SirBramble/The-Macruwu-2.0/PCB/The Macruwu 2.0/Seeeduino XIAO KICAD/XIAO-ESP32C3-DXF/113991054/top.dxf

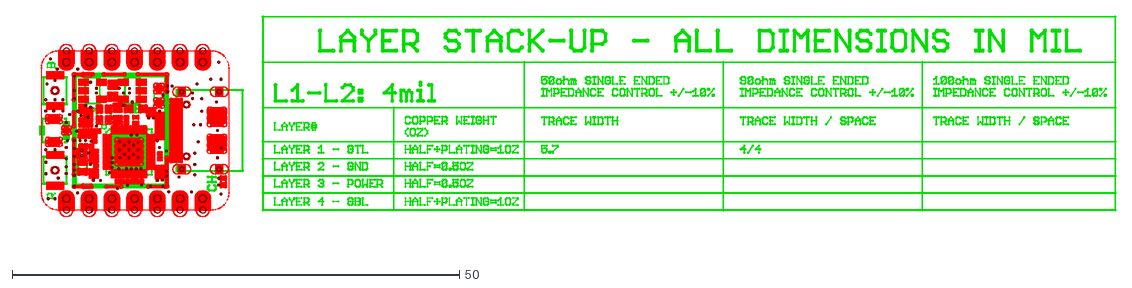
[picture p24: CAD file, 2023-02-24]
PCB/The Macruwu 2.0/Seeeduino XIAO KICAD/XIAO-ESP32C3-DXF/113991054/top.dxf
122.9 x 25.9
