SirBramble/The-Macruwu-2.0/3D Moddels/Case/Base no battery/Part1 no headphone.STL

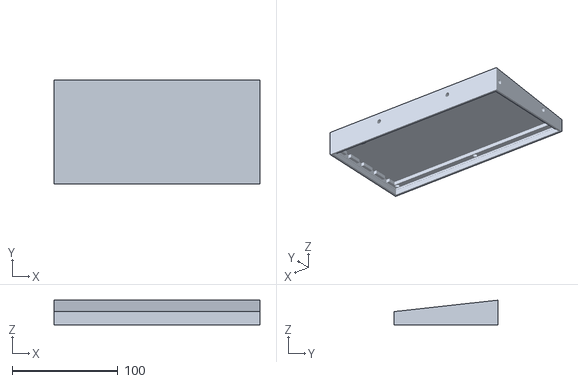
[picture p25: CAD file, 2024-02-04]
3D Moddels/Case/Base no battery/Part1 no headphone.STL
195.0 x 98.3 x 23.4
