SirBramble/The-Macruwu-2.0/3D Moddels/Case/Base/Plate.SLDPRT

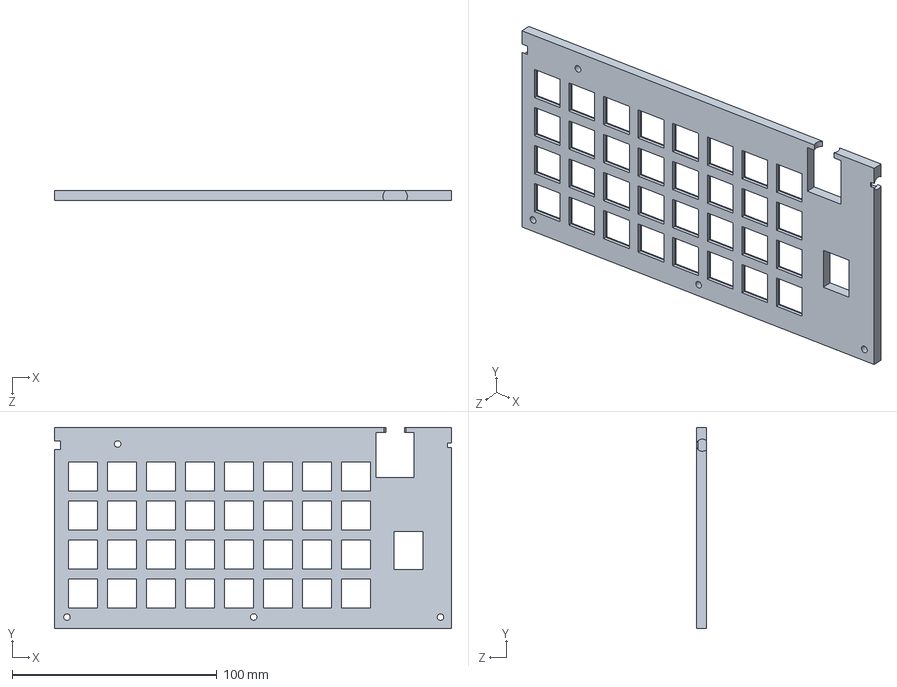
[picture p26: CAD file, 2023-02-24]
3D Moddels/Case/Base/Plate.SLDPRT
194.0 x 98.3 x 4.80 mm
