SirBramble/The-Macruwu-2.0/3D Moddels/Case/Base no battery/Part1.SLDPRT

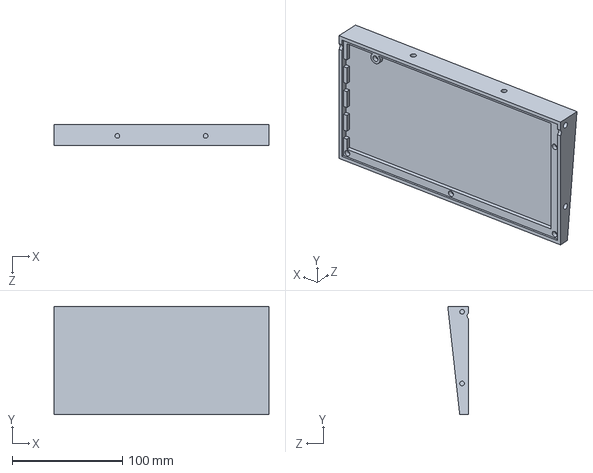
[picture p27: CAD file, 2024-02-04]
3D Moddels/Case/Base no battery/Part1.SLDPRT
195.0 x 98.3 x 18.6 mm
