SirBramble/The-Macruwu-2.0/3D Moddels/Case/Base/LED Cover.SLDPRT

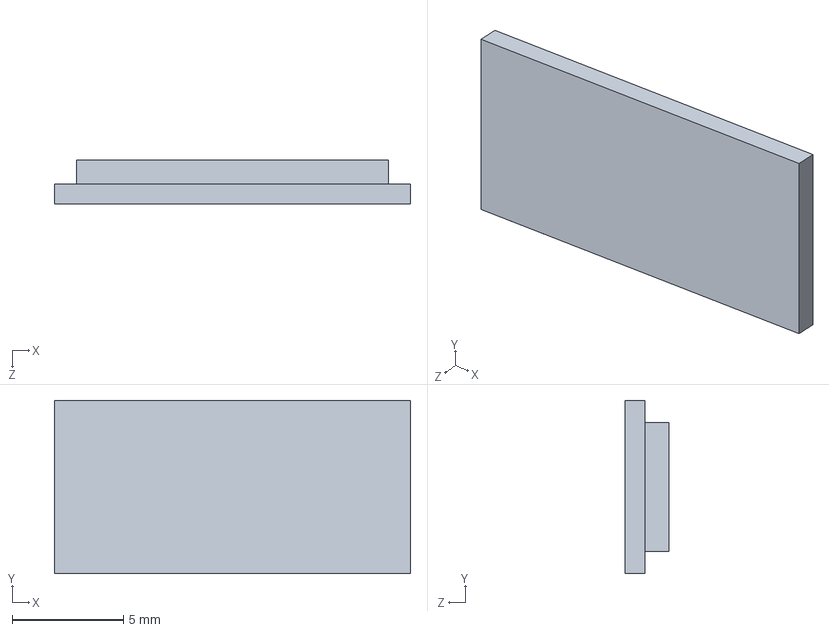
[picture p28: CAD file, 2023-02-24]
3D Moddels/Case/Base/LED Cover.SLDPRT
16.0 x 7.80 x 2.00 mm
